stsrc/stm32_nrf24l01/stm32f031f6_master/src/NRF24.h

#ifndef _NRF24_H_
#define _NRF24_H_
#include "SPI.h"
#include <stdbool.h>

struct nrf24 {
	SPI_HandleTypeDef spi_handler;
	SPI_TypeDef *spi_instance;
	uint32_t csn;
	uint32_t ce;
	uint32_t irq;
	GPIO_TypeDef *gpio;
};

void NRF24_init(struct nrf24 *nrf);
void NRF24_init_receiver(struct nrf24 *nrf);
bool NRF24_receiver_receive(struct nrf24 *nrf, uint8_t *buffer, size_t bufferSize);
#endif
