stsrc/stm32_nrf24l01/stm32f031f6_master/src/SPI.h

#ifndef _SPI_H_
#define _SPI_H_

#include <stdlib.h>
#include <string.h>
#include <stm32f0xx_hal_gpio.h>
#include <stm32f0xx_hal_rcc.h>
#include <stm32f0xx_hal_dma.h>
#include <stm32f0xx_hal_spi.h>
#include <stm32f0xx_hal_cortex.h>

/**
 * @addtogroup RFID_System libraries
 * @{
 */

/**
 * @defgroup SPI
 * @brief SPI library.
 * @{
 *
 * SPI library, which is based on HAL SPI library.
 */

/**
 * @brief Function presents that SPI result failed, by switching on LEDs.
 * @{
 * If error occures, execution of program is stoped.
 */
void SPI_show_error(HAL_StatusTypeDef rt);

HAL_StatusTypeDef SPI_init(SPI_HandleTypeDef *spi_handler, SPI_TypeDef *SPI);
HAL_StatusTypeDef SPI_send_multiple(SPI_HandleTypeDef *spi_handler,
				    uint8_t *data, uint8_t size);
HAL_StatusTypeDef SPI_send(SPI_HandleTypeDef *spi_handler, uint8_t *data);
HAL_StatusTypeDef SPI_send_and_receive(SPI_HandleTypeDef *spi_handler,
				       uint8_t data, uint8_t *receiveData);
HAL_StatusTypeDef SPI_read(SPI_HandleTypeDef *spi_handler, uint8_t *data,
			   uint16_t bytes);

#endif

/* TODO unification ! */
