stsrc/stm32_nrf24l01/stm32f031f6_slave/src/simple_buffer.h

/*
 * where-is-catiusha - cat localisation project
 * Copyright (C) 2021 Konrad Gotfryd
 *
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
 * You should have received a copy of the GNU General Public License
 * along with this program; if not, write to the Free Software
 * Foundation, Inc., 51 Franklin Street, Fifth Floor, Boston, MA  02110-1301, USA.
 */

#ifndef _SIMPLE_BUFFER_H_
#define _SIMPLE_BUFFER_H_
#include <stdint.h>
#include <stdlib.h>
#include <errno.h>
#include <string.h>

/**
 * @brief macros to set size of buffers at compile time
 */
#define BUF_MEM_SIZE 512

/**
 * @addtogroup RFID_System libraries
 * @{
 */

/**
 * @defgroup simple_buffer
 * @brief simple circural buffer library.
 *
 * @{
 *
 * Used by UART2 and esp8266 libraries.
 */


/**
 * @brief - simple_buffer struct, represents buffer.
 * @param lock variable as a mutex
 * @param temp temporary buffer used when lock is locked.
 * @param memory main buffer
 * @param head head of circular buffer
 * @param tail tail of circular buffer
 * @ignore count of bytes to ignore.
 */
struct simple_buffer{
	volatile uint8_t lock;
	char memory[BUF_MEM_SIZE];
	size_t head;
	size_t tail;
};

/**
 * @brief initalization of buffer.
 */
void buffer_init(struct simple_buffer *buf);

/**
 * @brief get byte from buffer. Returns byte by pointer.
 * @retval int8_t 0 on success. -ENOMEM if there is no bytes to read.
 */
int8_t buffer_get_byte(struct simple_buffer* buf, uint8_t *byte);

/**
 * @brief set byte to buffer.
 * @retval int8_t 0 on succes. -ENOMEM if there is no space.
 */
int8_t buffer_set_byte(struct simple_buffer* buf, uint8_t byte);

/**
 * @brief set data to buffer.
 * @param text data to set.
 * @param data_size data_size.
 * @retval int8_t 0 if success, -ENOMEM if there is no space.
 */
int8_t buffer_set_text(struct simple_buffer *buf, const char *text,
		       size_t data_size);

/**
 * @brief function for searching of some text. If function found label,
 * it copies to output buffer string from that label to limiter.
 * @param label text to search and from which start coping.
 * @param limiter text that ends coping.
 * @param output buffer in which text is placed.
 * @retval 0 on success, negative error otherwise.
 */
int8_t buffer_SearchGetLabel(struct simple_buffer *buf, const char *label,
			     const char *limiter, char *output, int8_t ignore_rn);

/**
 * @brief function checks wether buffer is full.
 * @retval 0 if it is not full, 1 otherwise.
 */
int8_t buffer_IsFull(struct simple_buffer *buf);

/**
 * @brief function which empties buffer.
 */
void buffer_Reset(struct simple_buffer *buf);

/**
 * @brief sets how many bytes to add will be ignored.
 */
void buffer_SetIgnore(struct simple_buffer *buf, size_t ignore);
#endif
